ChesneyBuyle/UltrasoundPhasedArray/Python/Measurement data/Beam steering patterns/beampattern_1x10_config_25kHz_0_75m_beamangle_0_anechoic_uncalibrated_v0_20210713-124206_info.txt

array_config: 1x10
frequency: 25kHz
distance: 0_75m
version: anechoic_uncalibrated_v0
beam_angle: 0
az_angle_step: 1
sample_rate: 400000
num_samples: 4095
num_samples_loops: 25
date_time: 20210713-124206.txt
