ChesneyBuyle/UltrasoundPhasedArray/Python/Measurement data/Beam steering patterns/beampattern_1x10_config_25kHz_0_75m_beamangle_70_anechoic_v0_20210713-181854_info.txt

array_config: 1x10
frequency: 25kHz
distance: 0_75m
version: anechoic_v0
beam_angle: 70
az_angle_step: 1
sample_rate: 400000
num_samples: 4095
num_samples_loops: 10
date_time: 20210713-181854.txt
