ChesneyBuyle/UltrasoundPhasedArray/Controller board code/Code/Src/matrix.c

/*  ____  ____      _    __  __  ____ ___
 * |  _ \|  _ \    / \  |  \/  |/ ___/ _ \
 * | | | | |_) |  / _ \ | |\/| | |  | | | |
 * | |_| |  _ <  / ___ \| |  | | |__| |_| |
 * |____/|_| \_\/_/   \_\_|  |_|\____\___/
 *                           research group
 *                             dramco.be/
 *
 *  KU Leuven - Technology Campus Gent,
 *  Gebroeders De Smetstraat 1,
 *  B-9000 Gent, Belgium
 *
 *         File: AD5270_71.c
 *      Created: 2020-07-30
 *       Author: Chesney Buyle
 *      Version: 1.0
 *
 *  Description: MEMS Speaker matrix
 *
 *  Commissiond by KU Leuven
 *
 *  License L (optionally)
 */
 
#include "matrix.h"


/*
	matrix configuration
	
	|1	5	 9	 13|
	|2	6	 10  14|
	|3	7  11  15|
	|4	8  12  16|
	
*/

/* 
const uint8_t mux_stages[4][4] = {
	{0x03, 0x01, 0x00, 0x00},
	{0x0B, 0x09, 0x00, 0x00},
	{0x0F, 0x00, 0x00, 0x00},
	{0x07, 0x00, 0x00, 0x00}
};

uint8_t teststage = 0;

void matrix_init(void){
	mux_init();
	
	AD9834_init();
	
	for (uint8_t i=0; i<1; i++){
		for (uint8_t j=0; i<1; i++){
			teststage = mux_stages[i][j];
			
			set_mux(mux_stages[i][j]);
			
			enable_mux();
			AD9834_set(0, 1000.0, 0.0);
			disable_mux();
		}
		
		AD9834_start();
	}	
	
	
	for (uint8_t i=0; i<1; i++){
		for (uint8_t j=0; i<1; i++){
			set_mux(mux_stages[i][j]);
			
			enable_mux();
			AD5270_71_init();
			disable_mux();
		}
	}
}
*/
